gbrickell/raspberrypi_maker_PCB/Raspberry_Pi_SBC_code/sensors/MPR121_touch_sensor/keyboard.py

# adapted for the RPi Maker PCB v5
# command:  python3 /home/pi/RPi_maker_PCB5/sensors/MPR121_touch_sensor/keyboard.py

# Adafruit Raspberry Pi MPR121 Keyboard Example
# Author: Tony DiCola
#
# Allows you to turn touches detected by the MPR121 into key presses on a
# Raspberry Pi.
#
# NOTE: This only works with a Raspberry Pi right now because it depends on some
# specific event detection logic in the RPi.GPIO library.
#
# Dependencies
# ============
#
# Make sure you have the required dependencies by executing the following commands:
#   sudo apt-get update
#   sudo apt-get install build-essential python-dev python-pip libudev-dev
#   sudo pip install python-uinput
#
# Also make sure you have installed the Adafruit Python MPR121 library by running
# its setup.py (in the parent directory):
#   sudo python setup.py install
#
# Usage
# =====
#
# To use this program you first need to connect the MPR121 board to the Raspberry
# Pi (either connect the HAT directly to the Pi, or wire the I2C pins SCL, SDA to
# the Pi SCL, SDA, VIN to Pi 3.3V, GND to Pi GND).  If you aren't using the HAT
# version of the board you must connect the IRQ pin to a free digital input on the
# Pi (the default is 26).
#
# Next define the mapping of capacitive touch input presses to keyboard
# button presses.  Scroll down to the KEY_MAPPING dictionary definition below
# and adjust the configuration as described in its comments.
#
# If you're using a differnet pin for the IRQ line change the IRQ_PIN variable
# below to the pin number you're using.  Don't change this if you're using the
# HAT version of the board as it's built to use pin 26 as the IRQ input.
#
# Finally run the script as root:
#   sudo python keyboard.py
#
# Try pressing buttons and you should see key presses made on the Pi!
#
# Press Ctrl-C to quit at any time.
#
# Copyright (c) 2014 Adafruit Industries
#
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
import Adafruit_MPR121.MPR121 as MPR121
import RPi.GPIO as GPIO
import uinput


# Define mapping of capacitive touch pin presses to keyboard button presses.
KEY_MAPPING = {
                0: uinput.KEY_UP,    # Each line here should define a dict entry
                1: uinput.KEY_DOWN,  # that maps the capacitive touch input number
                2: uinput.KEY_LEFT,  # to an appropriate key press.
                3: uinput.KEY_RIGHT, #
                4: uinput.KEY_B,     # For reference the list of possible uinput.KEY_*
                5: uinput.KEY_A,     # values you can specify is defined in linux/input.h:
                6: uinput.KEY_ENTER, # http://www.cs.fsu.edu/~baker/devices/lxr/http/source/linux/include/linux/input.h?v=2.6.11.8
                7: uinput.KEY_SPACE, #
              }                      # Make sure a cap touch input is defined only
                                     # once or else the program will fail to run!

# Input pin connected to the capacitive touch sensor's IRQ output.
# For the capacitive touch HAT this should be pin 26!
IRQ_PIN = 26

# Don't change the below values unless you know what you're doing.  These help
# adjust the load on the CPU vs. responsiveness of the key detection.
MAX_EVENT_WAIT_SECONDS = 0.5
EVENT_WAIT_SLEEP_SECONDS = 0.1


# Uncomment to enable debug message logging (might slow down key detection).
#logging.basicConfig(level=logging.DEBUG)

# Make sure uinput kernel module is loaded.
subprocess.check_call(['modprobe', 'uinput'])

# Configure virtual keyboard.
device = uinput.Device(KEY_MAPPING.values())

# Setup the MPR121 device.
cap = MPR121.MPR121()
if not cap.begin():
    print('Failed to initialize MPR121, check your wiring!')
    sys.exit(1)

# Configure GPIO library to listen on IRQ pin for changes.
# Be sure to configure pin with a pull-up because it is open collector when not
# enabled.
GPIO.setmode(GPIO.BCM)
GPIO.setup(IRQ_PIN, GPIO.IN, pull_up_down=GPIO.PUD_UP)
GPIO.add_event_detect(IRQ_PIN, GPIO.FALLING)
atexit.register(GPIO.cleanup)

# Clear any pending interrupts by reading touch state.
cap.touched()

# Event loop to wait for IRQ pin changes and respond to them.
print('Press Ctrl-C to quit.')
while True:
    # Wait for the IRQ pin to drop or too much time ellapses (to help prevent
    # missing an IRQ event and waiting forever).
    start = time.time()
    while (time.time() - start) < MAX_EVENT_WAIT_SECONDS and not GPIO.event_detected(IRQ_PIN):
        time.sleep(EVENT_WAIT_SLEEP_SECONDS)
    # Read touch state.
    touched = cap.touched()
    # Emit key presses for any touched keys.
    for pin, key in KEY_MAPPING.iteritems():
        # Check if pin is touched.
        pin_bit = 1 << pin
        if touched & pin_bit:
            # Emit key event when touched.
            logging.debug('Input {0} touched.'.format(pin))
            device.emit_click(key)
